ID6763Fall2016/Transitnotifier_RedGuppy/IMG_20161011_123356.jpg

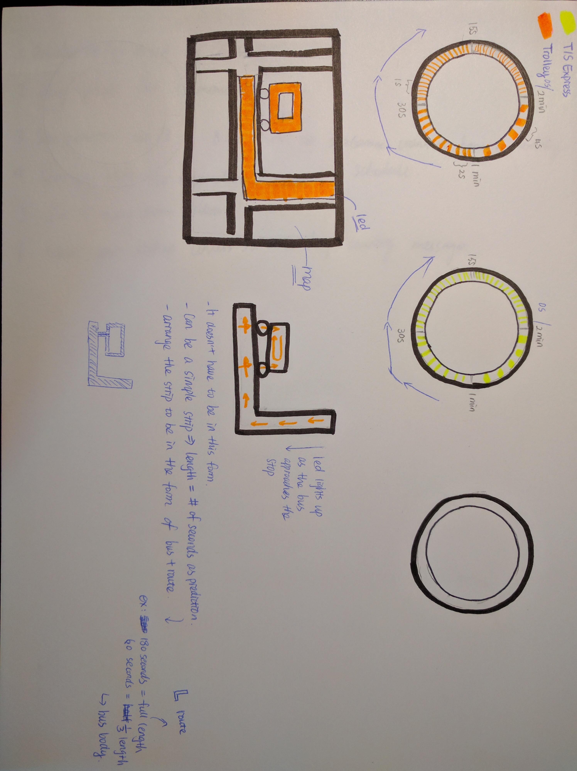
IMG_20161011_123356.jpg
